anitaraluca/Proiect_TSC/EBook_Reader/Images/pcb+display.png

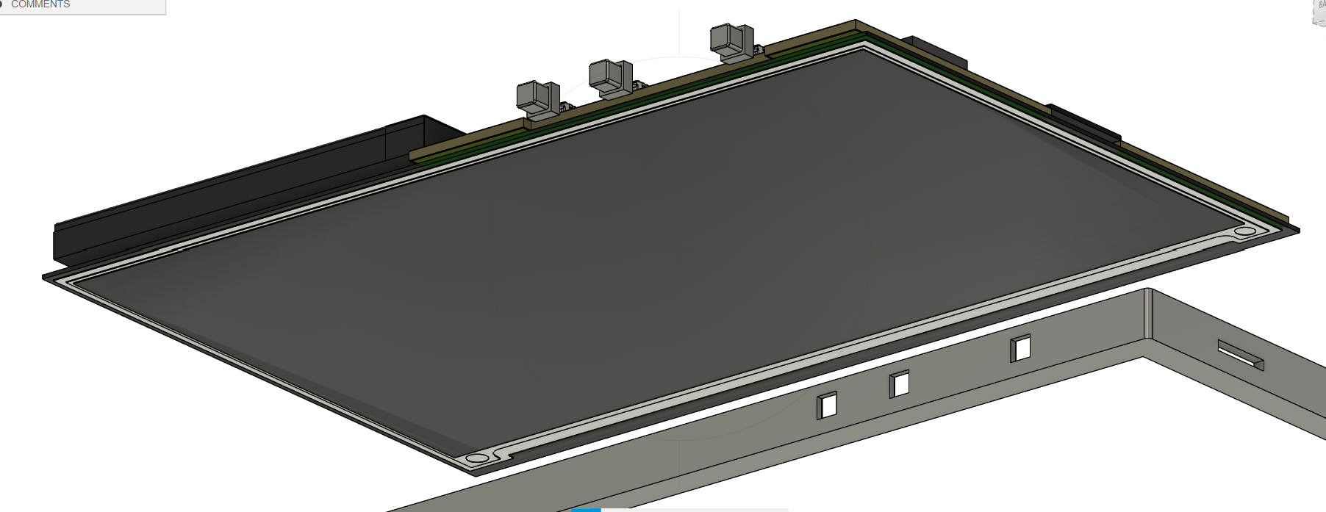
EBook_Reader/Images/pcb+display.png
